Sanadofe/SIXzero/PICTURES/SIX-zero back compo.png

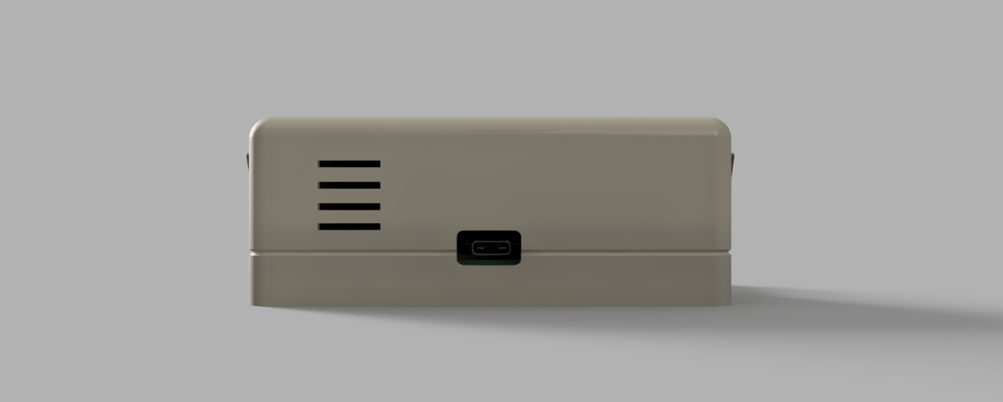
PICTURES/SIX-zero back compo.png
